justinnova0915/fallout/Fallout_UI/34/0.jpg

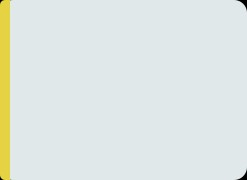
Fallout_UI/34/0.jpg
