justinnova0915/fallout/Fallout_UI/Assets/bg/Workspace_background_transition/00WorkspaceBackground.png

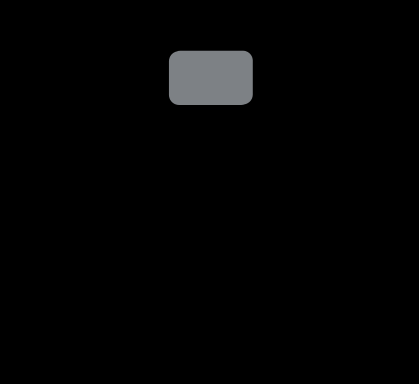
Fallout_UI/Assets/bg/Workspace_background_transition/00WorkspaceBackground.png
