justinnova0915/fallout/Fallout_UI/Assets/bg/Workspace_background_transition/02WorkspaceBackground.png

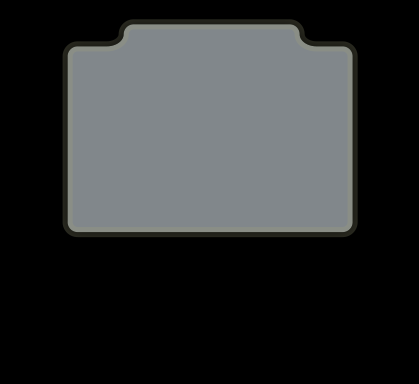
Fallout_UI/Assets/bg/Workspace_background_transition/02WorkspaceBackground.png
